michalfratczak/pizero_tracker/tracker/code/main/GLOB.h

#pragma once

#include <string>
#include <vector>
#include <map>
#include <atomic>
#include <chrono>

#include "mtx2/mtx2.h"
#include "nmea/nmea.h"
#include "dynamics_t.h"


enum class flight_state_t : int
{
	kUnknown = 0,
	kStandBy = 1, // near launch position and average abs(dAlt/dTime) < 3 m/s
	kAscend = 2,  // average dAlt/dTime > 3 m/s
	kDescend = 3, // average dAlt/dTime < -3 m/s
	kFreefall = 4, // average abs(dAlt/dTime) < -8 m/s
	kLanded = 5 // far from launch position and average abs(dAlt/dTime) < 3 m/s and alt<2000
};


// global options - singleton
class GLOB
{

private:
    GLOB() {};
    GLOB( const GLOB& ) = delete; // non construction-copyable
    GLOB& operator=( const GLOB& ) = delete; // non copyable

    std::atomic<nmea_t> nmea_; // GPS data
    std::atomic<nmea_t> nmea_last_valid_; // GPS data - last valid
    std::chrono::steady_clock::time_point gps_fix_timestamp_;

    // sensors dynamics
    std::map<std::string, dynamics_t>    dynamics_; // index: value name (alt, temp1, etc.)

    // flight state
    std::atomic<flight_state_t>  flight_state_{flight_state_t::kUnknown};

public:
    static GLOB& get()
    {
        static GLOB g;
        return g;
    }

    struct cli_t // command line interface options
    {
        std::string     callsign;
        float           freqMHz = 0;    //MegaHertz
        baud_t          baud = baud_t::kInvalid;
        std::string     ssdv_image;     // ssdv encoded image path
        std::string     logsdir{"./"};        // logs dirs
        int             msg_num = 5;    // number of telemetry sentences emitted between SSDV packets
        int             port = 6666;    // zeroMQ server port
        float           lat = 0;    // launch site latitude deg
        float           lon = 0;    // launch site longitude deg
        float           alt = 0;    // launch site altitude meters
        bool            testgps = false;   // generate fake GPS for testing
        bool            watchdog = false;  // enable watchdog

        // hardware config
        int             hw_pin_radio_on = 0;    // gpio numbered pin for radio enable. current board: 22
        std::string     hw_radio_serial;        // serial device for MTX2 radio. for rPI4: /dev/serial0
        std::string     hw_ublox_device;        // I2C device for uBLOX. for rPI4: /dev/i2c-7
    };
    cli_t cli;

    void        dynamics_add(const std::string& name, const dynamics_t::tp timestamp, const float value);
    dynamics_t  dynamics_get(const std::string& name) const;
    std::vector<std::string>  dynamics_keys() const; // names in dynamics_

    void nmea_set(const nmea_t& in_nmea) {
        get().nmea_ = in_nmea;
        if(in_nmea.valid()) {
            get().nmea_last_valid_ = in_nmea;
            get().gps_fix_now();
        }
    }

    nmea_t  nmea_current() { nmea_t ret = get().nmea_; return ret; }
    nmea_t  nmea_last_valid()   { nmea_t ret = get().nmea_last_valid_; return ret; }

    void gps_fix_now() { gps_fix_timestamp_ = std::chrono::steady_clock::now(); }
    int  gps_fix_age() const { return (std::chrono::steady_clock::now() - gps_fix_timestamp_).count() / 1e9; }

    void flight_state_set(const flight_state_t flight_state) { get().flight_state_ = flight_state; }
    flight_state_t flight_state_get() const { return get().flight_state_; }

    // runtime seconds
    long long runtime_secs_ = 0;
    std::string runtime_str() const; // return runtime in format HH:MM:SS

    std::string str() const;

};
